theapi/esp8266wsn/transmitter/hardware/ltspice/filter.asc

C1: cap; 1µf
R1: res; 1k
V1: voltage; PULSE(0 3.3 0 1us 1us 25ms 50ms)
Named nets: 0, out
.tran 50ms
