theapi/esp8266wsn/receiver/software/main/app_main.c

/**
 * WSN Receiver
 */

#include "freertos/FreeRTOS.h"
#include "freertos/timers.h"

#include "driver/uart.h"

#include "display.h"
#include "payload.h"
#include "network.h"
#include "light.h"
#include "display_payload.h"

//static const char *TAG = "receiver";

void app_main(void) {
  Display_init();

  // Configure ADC after the SPI
  if (Light_init() != ESP_OK) {
    esp_restart();
  }

  // Configure parameters of an UART driver,
  // communication pins and install the driver
  uart_config_t uart_config = {
      .baud_rate = 115200,
      .data_bits = UART_DATA_8_BITS,
      .parity    = UART_PARITY_DISABLE,
      .stop_bits = UART_STOP_BITS_1,
      .flow_ctrl = UART_HW_FLOWCTRL_DISABLE
  };
  uart_param_config(UART_NUM_0, &uart_config);
  uart_driver_install(UART_NUM_0, UART_BUF_SIZE * 2, 0, 0, NULL);

  if (Network_init() != ESP_OK) {
    esp_restart();
  }

  if (Light_start() != ESP_OK) {
    esp_restart();
  }

  hdisplay.pixels = 0xFFFF;
  Display_update(&hdisplay);

  if (DisplayPayload_start() != ESP_OK) {
    esp_restart();
  }

  if (Network_start() != ESP_OK) {
    esp_restart();
  }

  // hdisplay.pixels = 1;
  // Display_update(&hdisplay);
  // while (1 != 2) {
  //   vTaskDelay(10 / portTICK_RATE_MS);
  //   hdisplay.pixels++;
  //   Display_update(&hdisplay);
  // }

}
